cecio/USBvalve/PCB/USBpipe/PCB_USBpipe_Rev1.x.png

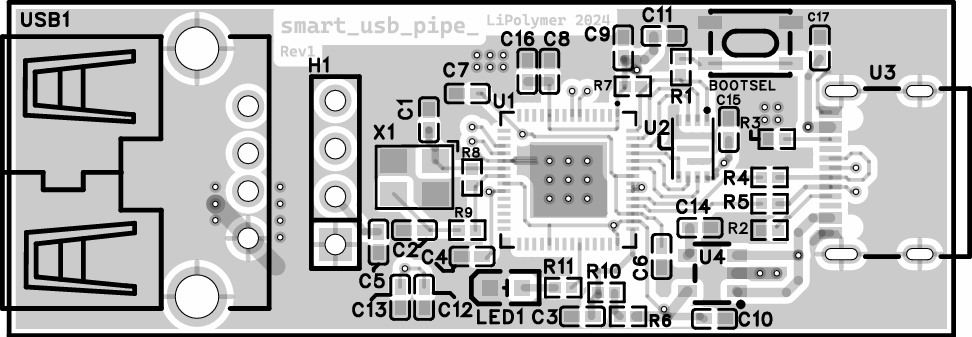
PCB/USBpipe/PCB_USBpipe_Rev1.x.png
