cecio/USBvalve/pictures/USB_pipe_finished.jpg

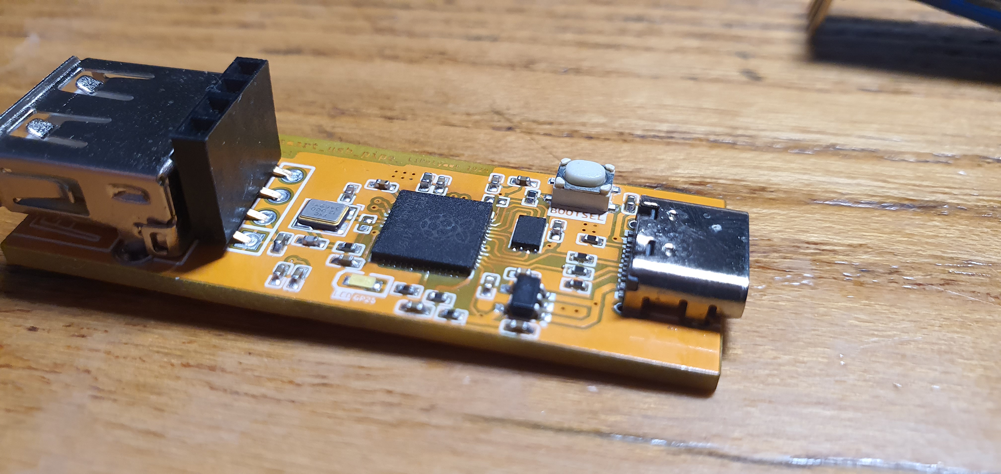
pictures/USB_pipe_finished.jpg
